YoussefAymanJo/Splitly/Firmware/vert_cat.bmp

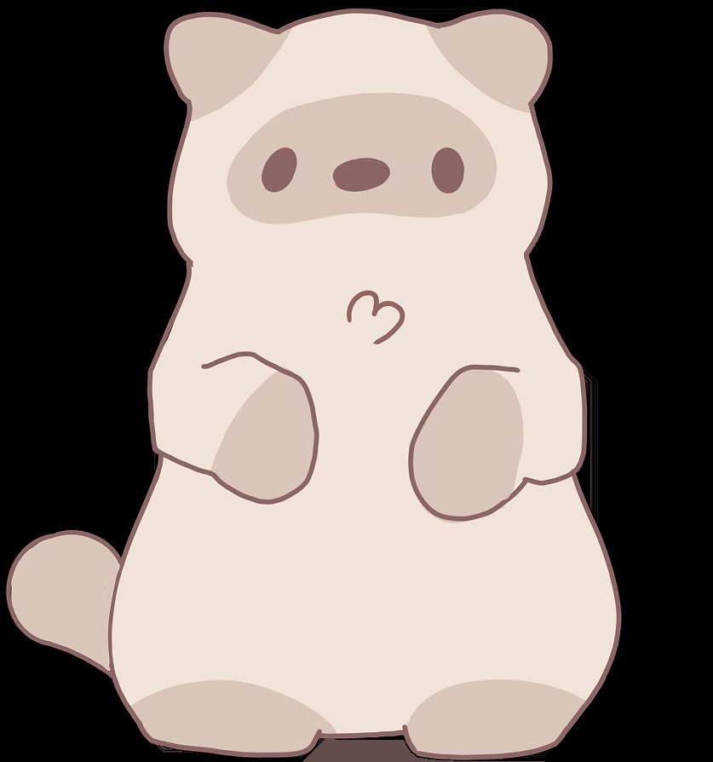
Firmware/vert_cat.bmp
