YoussefAymanJo/Splitly/images/corne,-default-layer.png

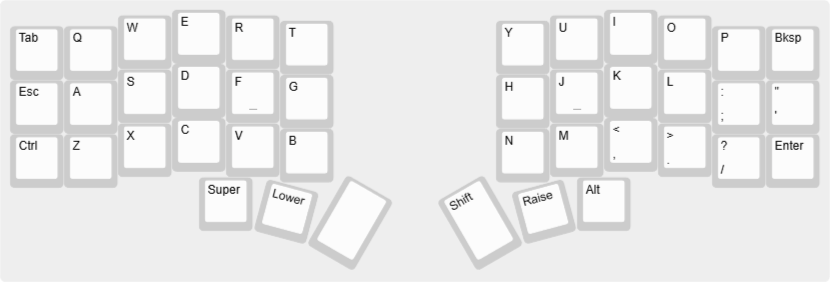
images/corne,-default-layer.png
