YoussefAymanJo/Splitly/images/Screenshot 2026-07-29 123833.png

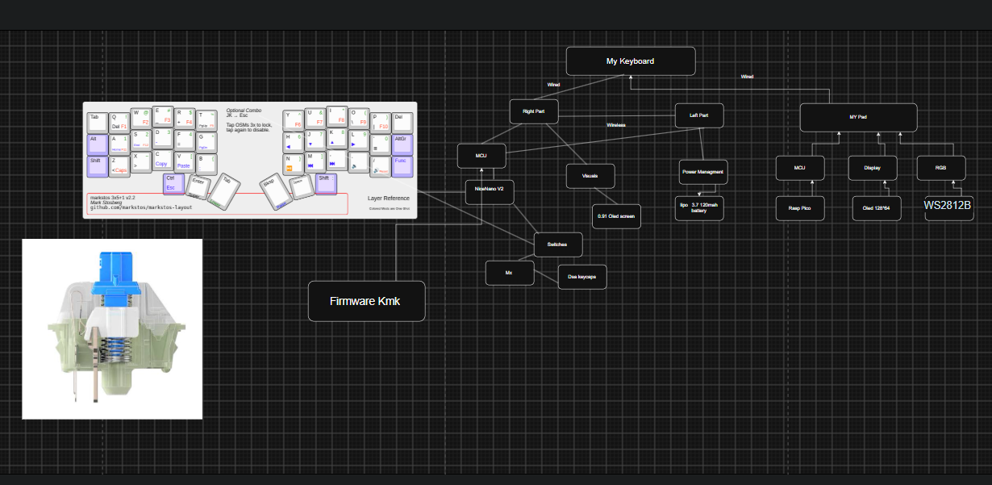
images/Screenshot 2026-07-29 123833.png
