YoussefAymanJo/Splitly/images/Screenshot 2026-07-29 131850.png

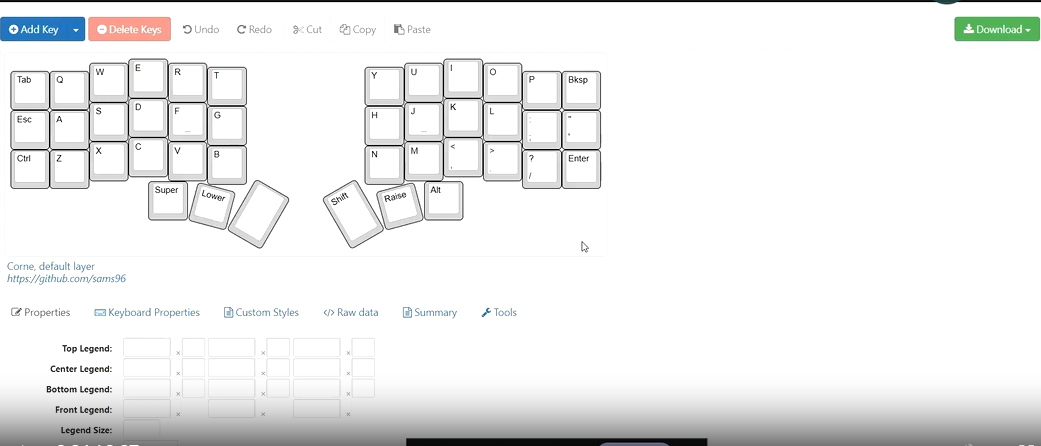
images/Screenshot 2026-07-29 131850.png
