YoussefAymanJo/Splitly/images/Screenshot 2026-07-29 140504.png

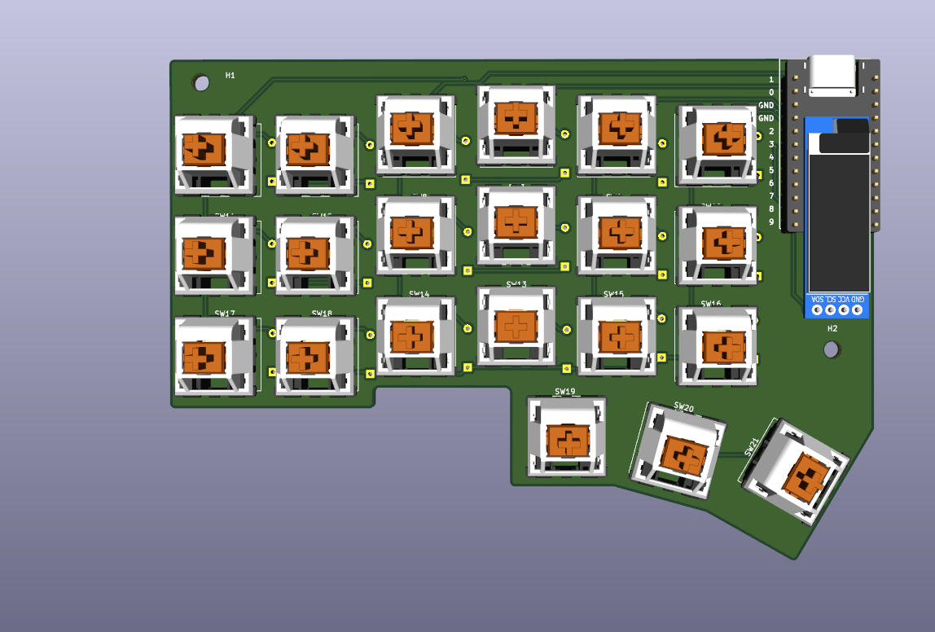
images/Screenshot 2026-07-29 140504.png
