YoussefAymanJo/Splitly/images/Screenshot 2026-07-29 140726.png

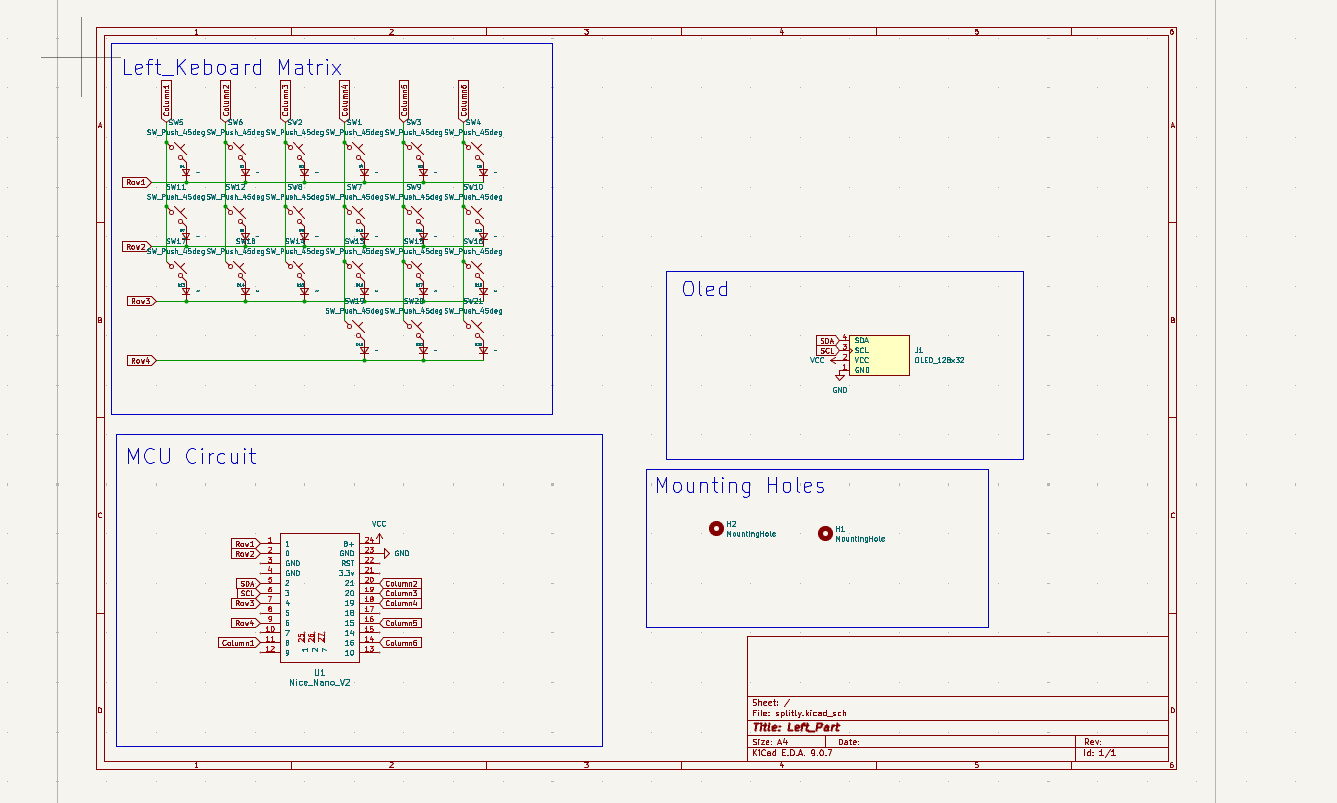
images/Screenshot 2026-07-29 140726.png
