YoussefAymanJo/Splitly/images/Screenshot 2026-07-29 143845.png

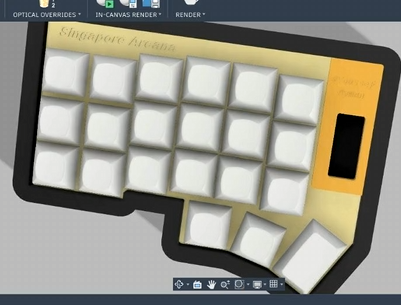
images/Screenshot 2026-07-29 143845.png
