YoussefAymanJo/Splitly/images/Screenshot 2026-07-29 144237.png

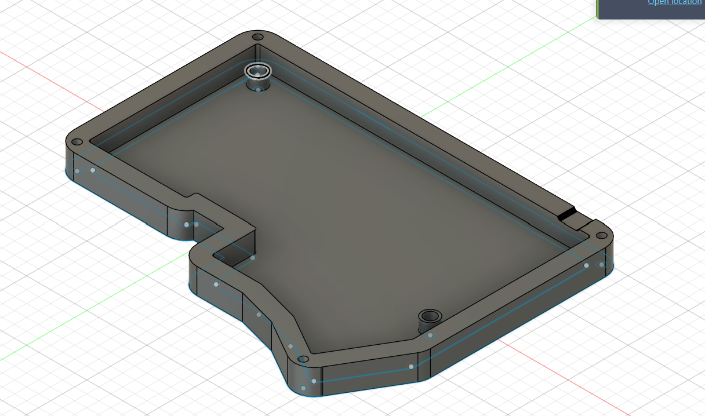
images/Screenshot 2026-07-29 144237.png
