YoussefAymanJo/Splitly/images/Screenshot 2026-07-29 151332.png

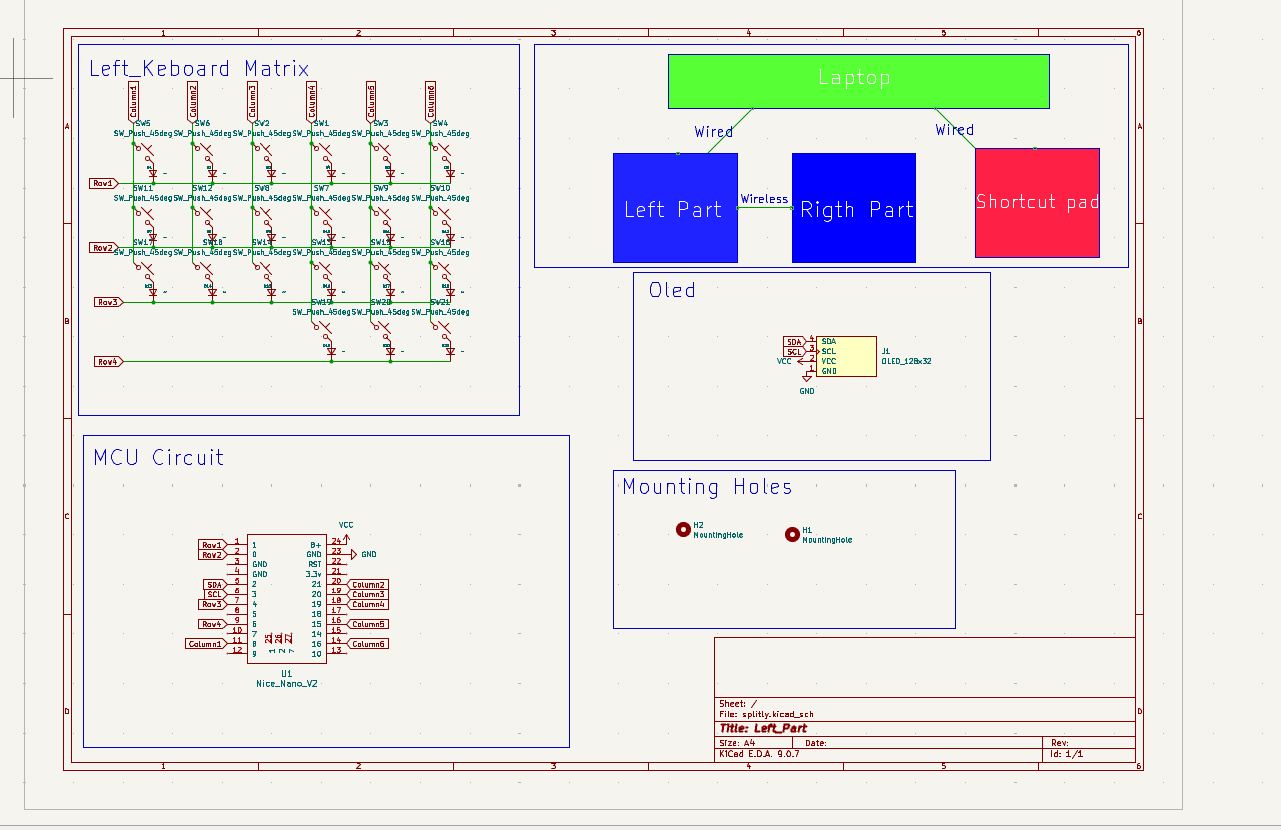
images/Screenshot 2026-07-29 151332.png
