YoussefAymanJo/Splitly/images/Screenshot 2026-07-29 151357.png

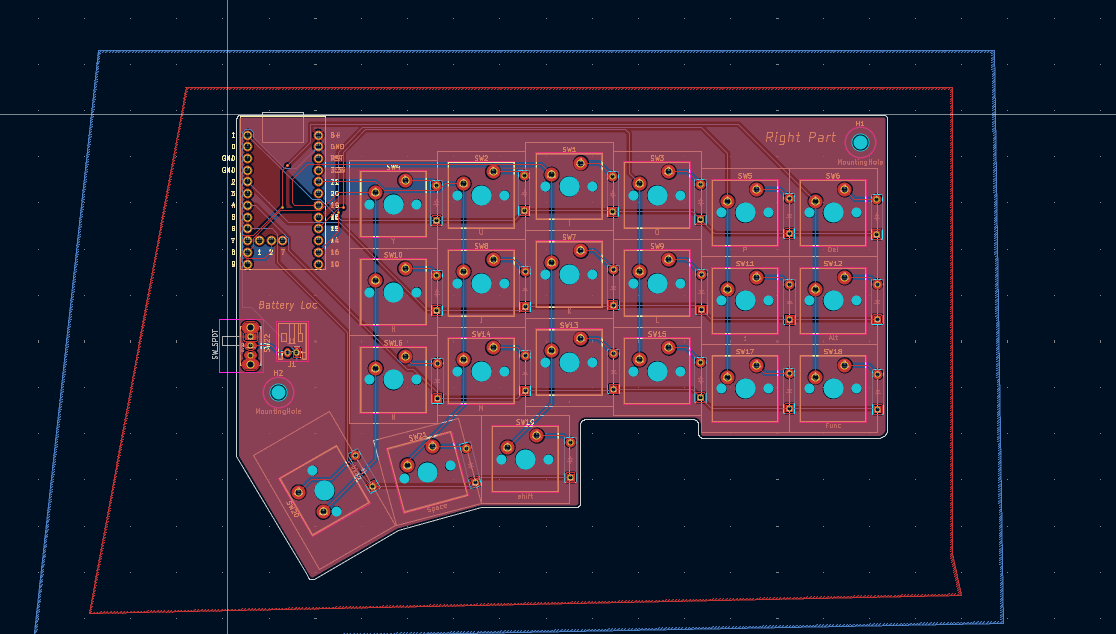
images/Screenshot 2026-07-29 151357.png
