YoussefAymanJo/Splitly/images/Screenshot 2026-07-29 151404.png

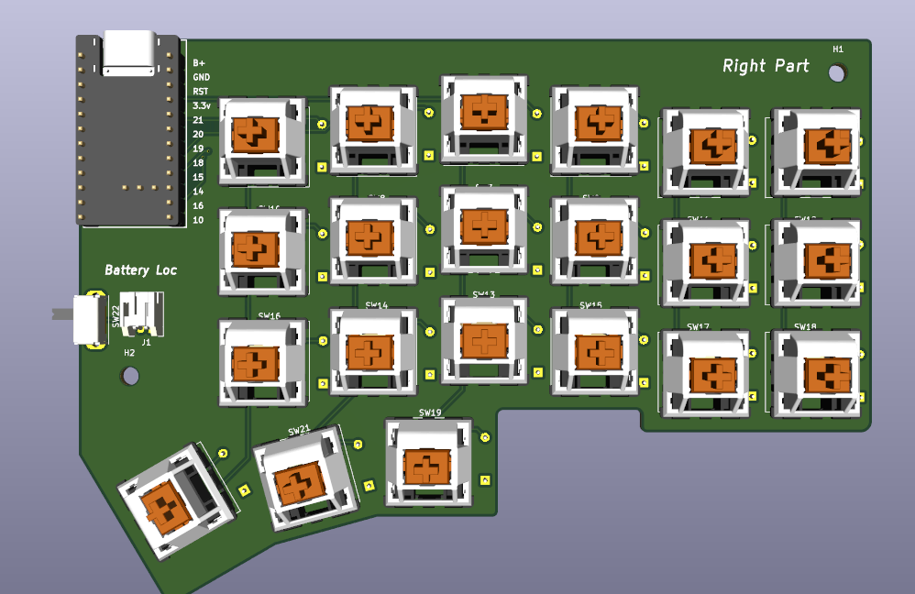
images/Screenshot 2026-07-29 151404.png
