YoussefAymanJo/Splitly/images/Screenshot 2026-07-29 154041.png

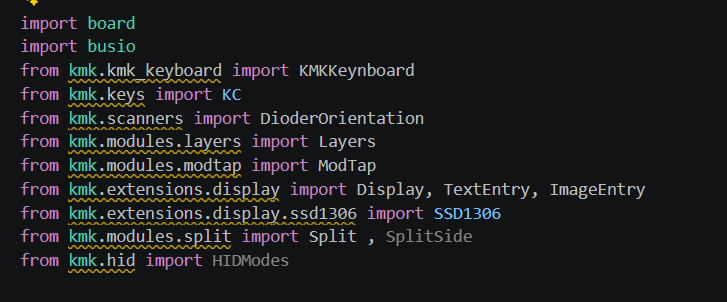
images/Screenshot 2026-07-29 154041.png
