YoussefAymanJo/Splitly/images/Screenshot 2026-07-29 154101.png

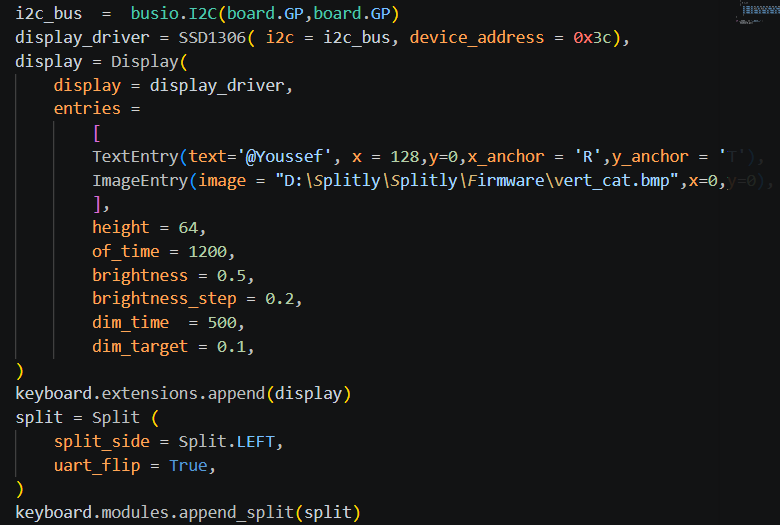
images/Screenshot 2026-07-29 154101.png
