YoussefAymanJo/Splitly/images/Screenshot 2026-07-29 154108.png

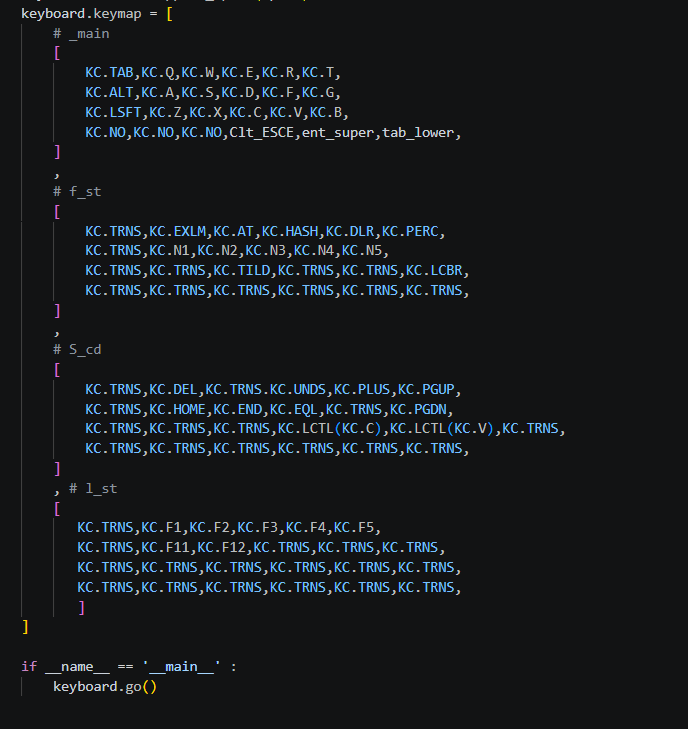
images/Screenshot 2026-07-29 154108.png
