YoussefAymanJo/Splitly/Production/Right_top_cover.step

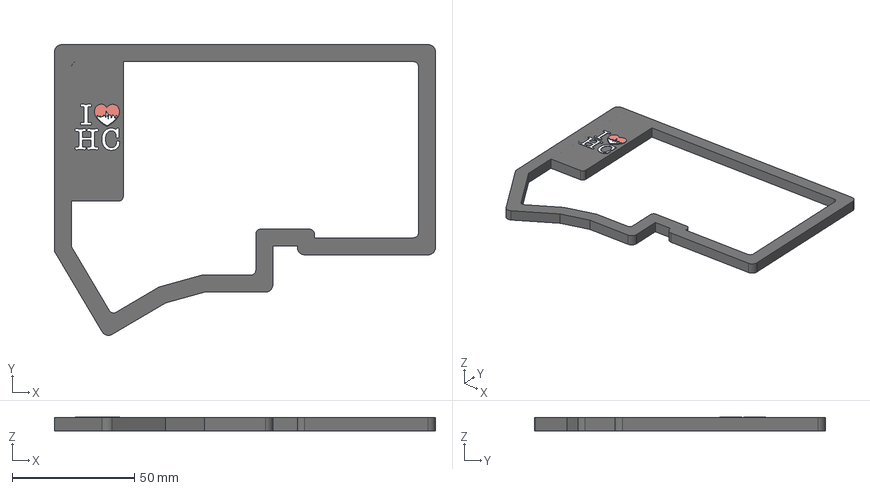
[picture p86: CAD file, 2026-07-18]
Production/Right_top_cover.step
155.9 x 119.0 x 5.75 mm
