YoussefAymanJo/Splitly/Production/M3 Threaded Insert_.step

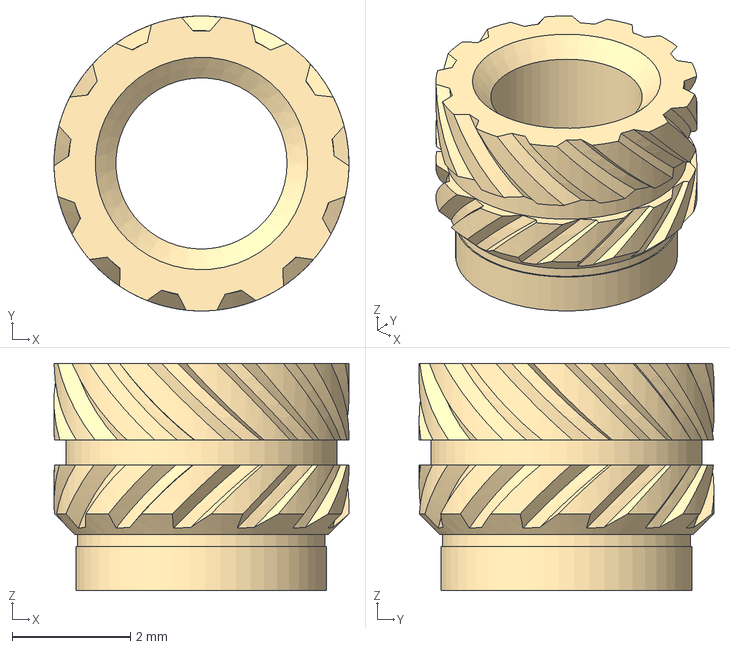
[picture p87: CAD file, 2026-07-18]
Production/M3 Threaded Insert_.step
5.00 x 5.00 x 3.85 mm
