YoussefAymanJo/Splitly/Production/Battery.step

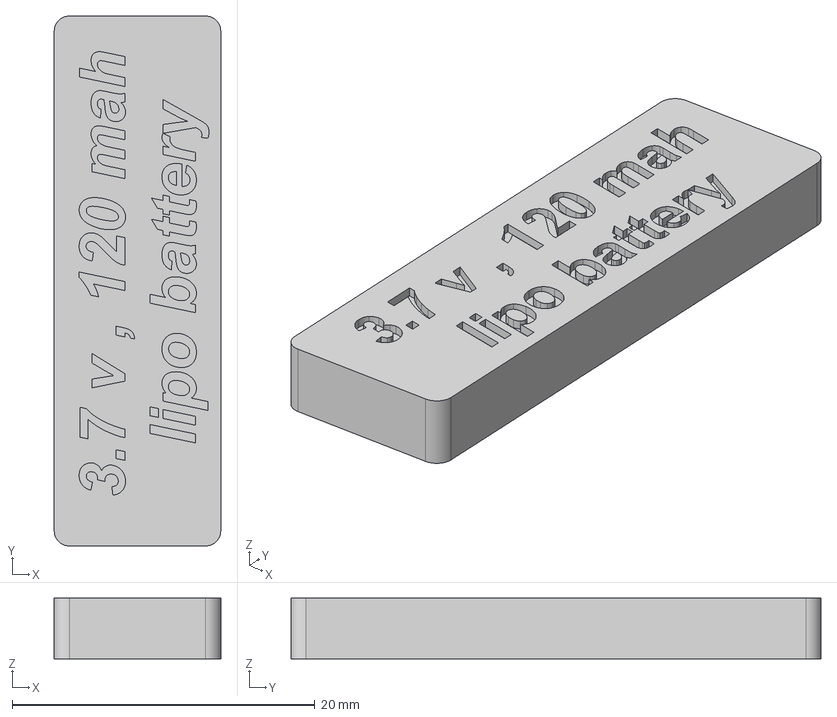
[picture p88: CAD file, 2026-07-18]
Production/Battery.step
11.0 x 35.0 x 4.00 mm
