YoussefAymanJo/Splitly/Production/right_part.step

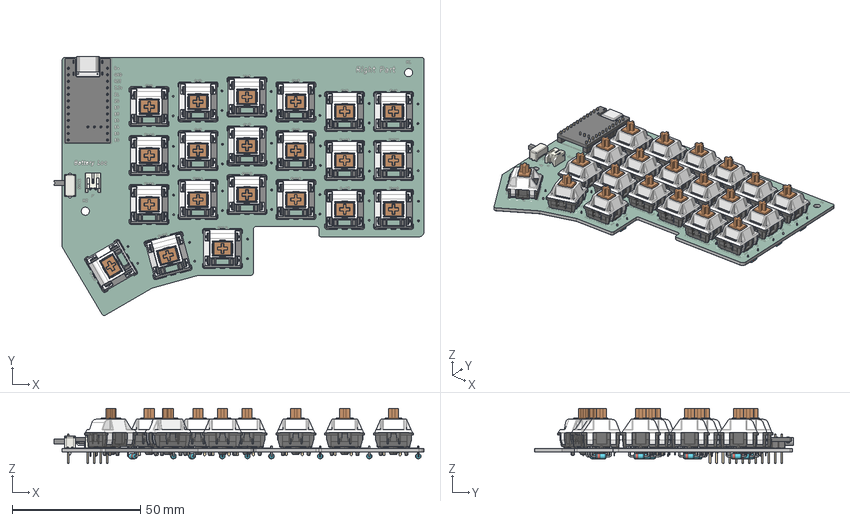
[picture p89: CAD file, 2026-07-17]
Production/right_part.step
144.2 x 100.9 x 21.5 mm
MX_PCB x 21
JST_PH_S2B-PH-K_1x02_P2.00mm_Horizontal
PinHeader_1x12_P2.54mm_Vertical.step
User Library-TYPE-C-31-M-14.step
MICRO_603 resistor 102
MICRO_stackable header pin x 12
MICRO_stackable header 12
micro_crystal 5x3
MICRO_led
micro_MIC5219
SW_Slide_SPDT_Angled_CK_OS102011MA1Q
Diode_DO-35 x 21
right_part_copper
right_part_via
right_part_silkscreen x 2
right_part_soldermask x 2
right_part_PCB
