YoussefAymanJo/Splitly/Production/splitly.step

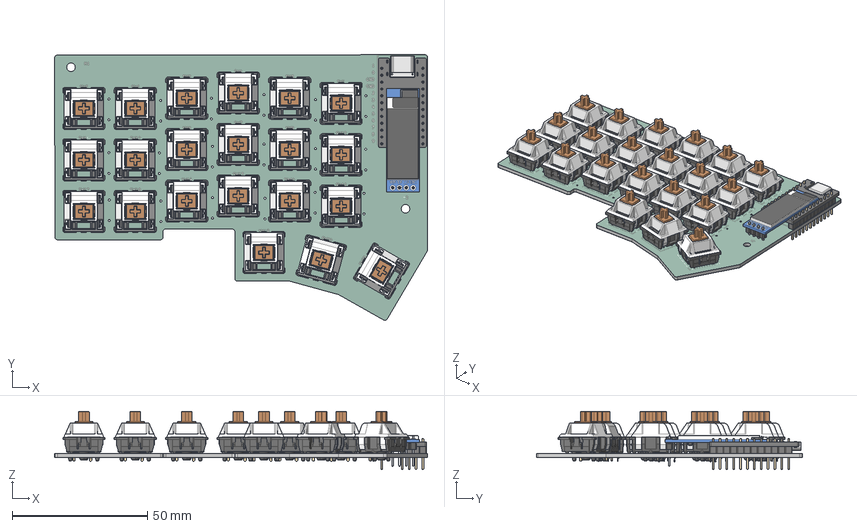
[picture p90: CAD file, 2026-07-16]
Production/splitly.step
138.1 x 98.3 x 21.5 mm
MX_PCB x 21
PinHeader_1x12_P2.54mm_Vertical.step
User Library-TYPE-C-31-M-14.step
MICRO_603 resistor 102
MICRO_stackable header pin x 12
MICRO_stackable header 12
micro_crystal 5x3
MICRO_led
micro_MIC5219
OLED_0.91_128x32
Pin Header 4 x 1 TH 2.54mm Pitch
RESC-0603 x 13
2SD0601A
splitly_silkscreen x 2
splitly_soldermask x 2
splitly_PCB
